CMeissner-creator/ANS-Projekt/Messungen/Oszillator_Bilder/TEK0000.JPG

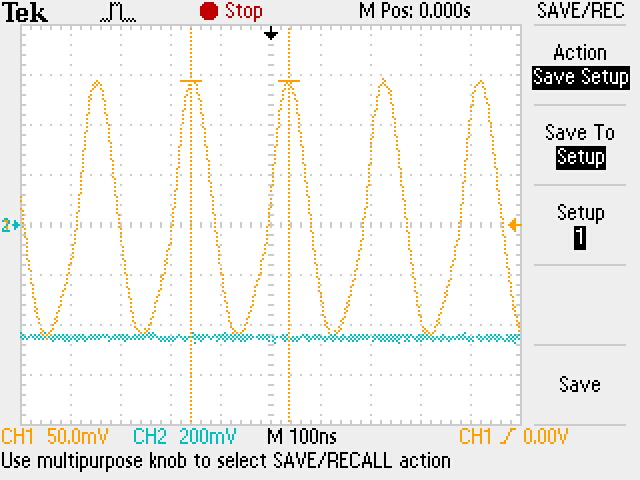
Messungen/Oszillator_Bilder/TEK0000.JPG
