CMeissner-creator/ANS-Projekt/Messungen/Oszillator_Bilder/TEK0003.JPG

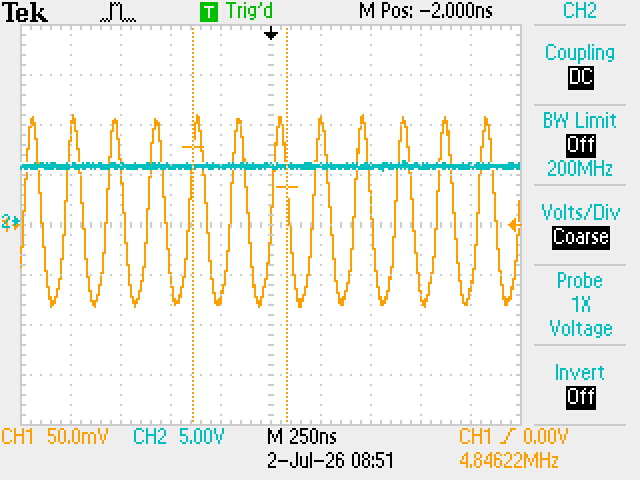
Messungen/Oszillator_Bilder/TEK0003.JPG
