CMeissner-creator/ANS-Projekt/Messungen/Oszillator_Bilder/TEK0005.JPG

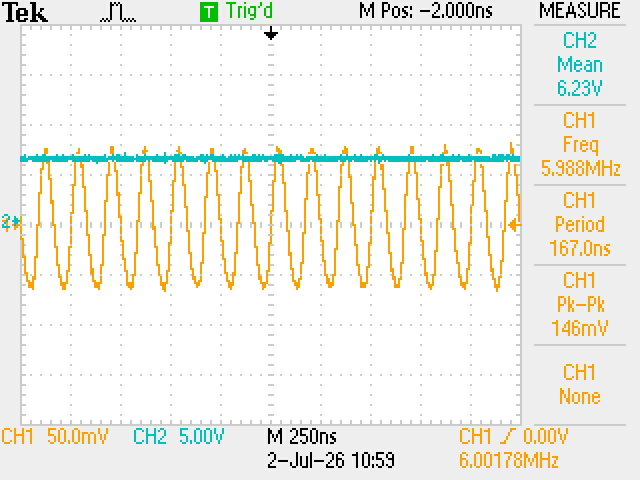
Messungen/Oszillator_Bilder/TEK0005.JPG
