CMeissner-creator/ANS-Projekt/Messungen/Oszillator_Bilder/TEK0006.JPG

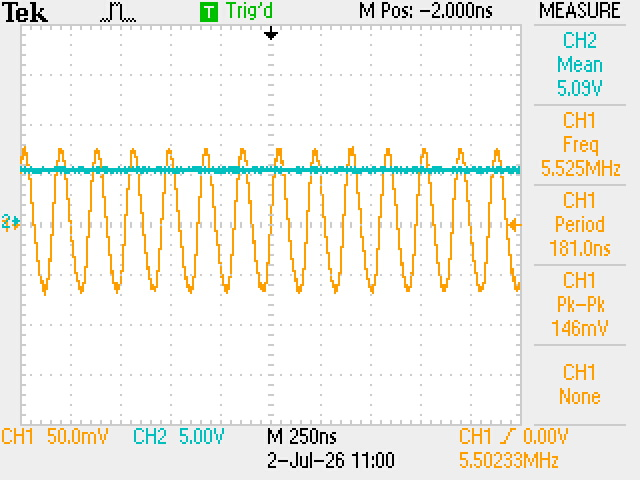
Messungen/Oszillator_Bilder/TEK0006.JPG
